Dermiste/Quadricopter/Cartes/InterfacesCapteurs/gyro/LPR430.png

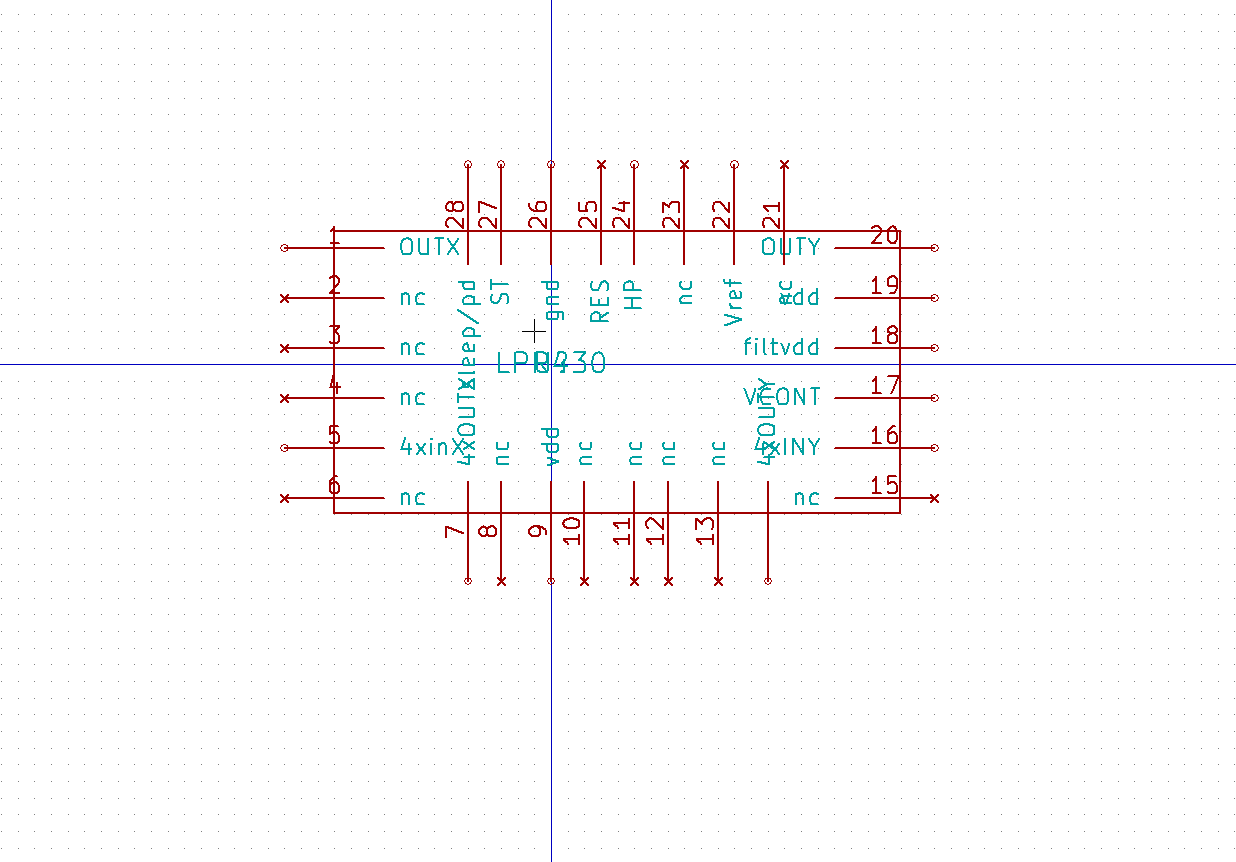
Cartes/InterfacesCapteurs/gyro/LPR430.png
