Dermiste/Quadricopter/ScilabScripts/DataTracer/ScreenShots/noise_2cylinbloc_2normal.png

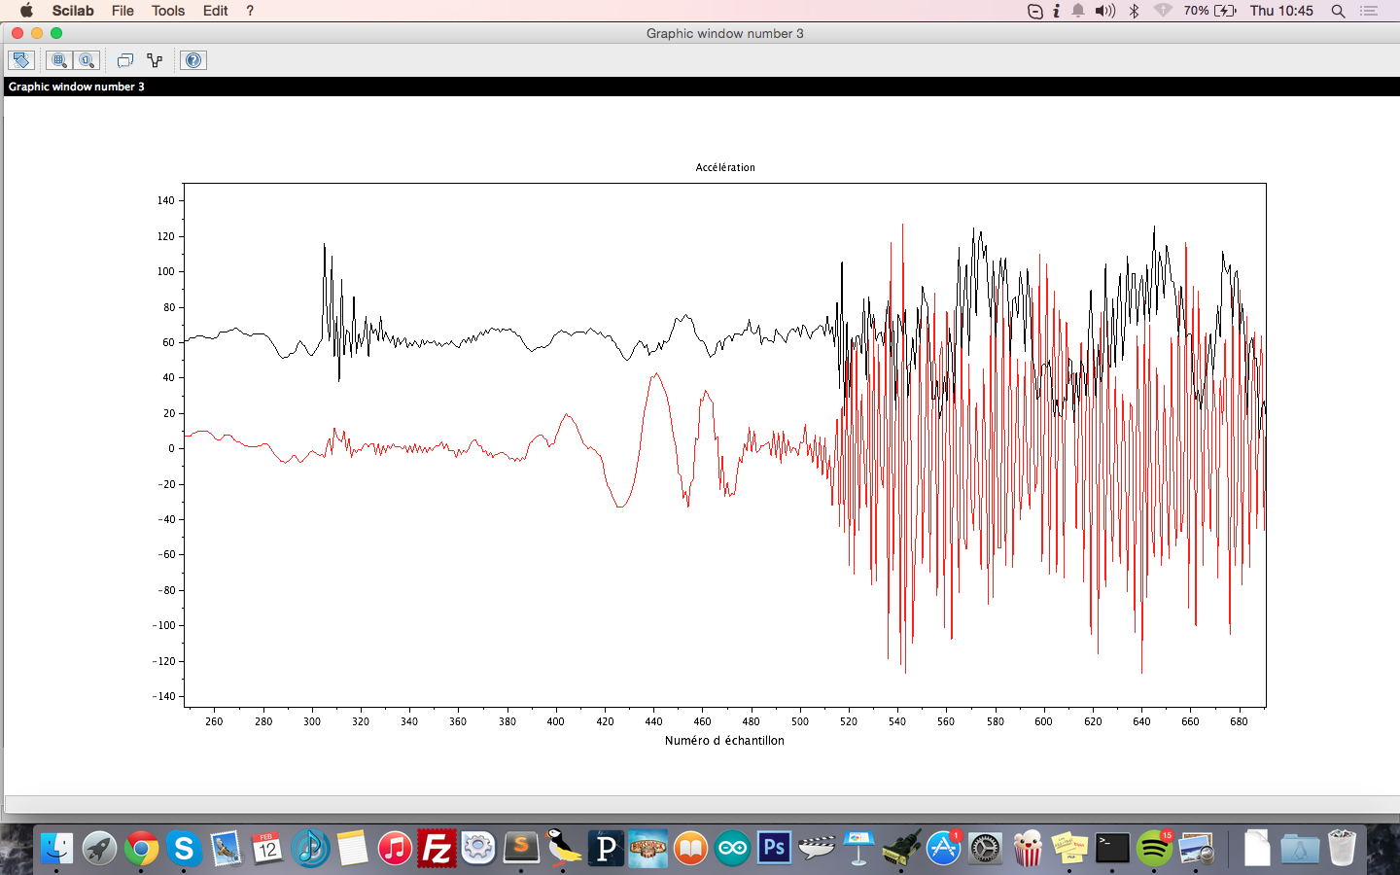
ScilabScripts/DataTracer/ScreenShots/noise_2cylinbloc_2normal.png
