Dermiste/Quadricopter/ScilabScripts/DataTracer/ScreenShots/noise_cylinbloc_axis.png

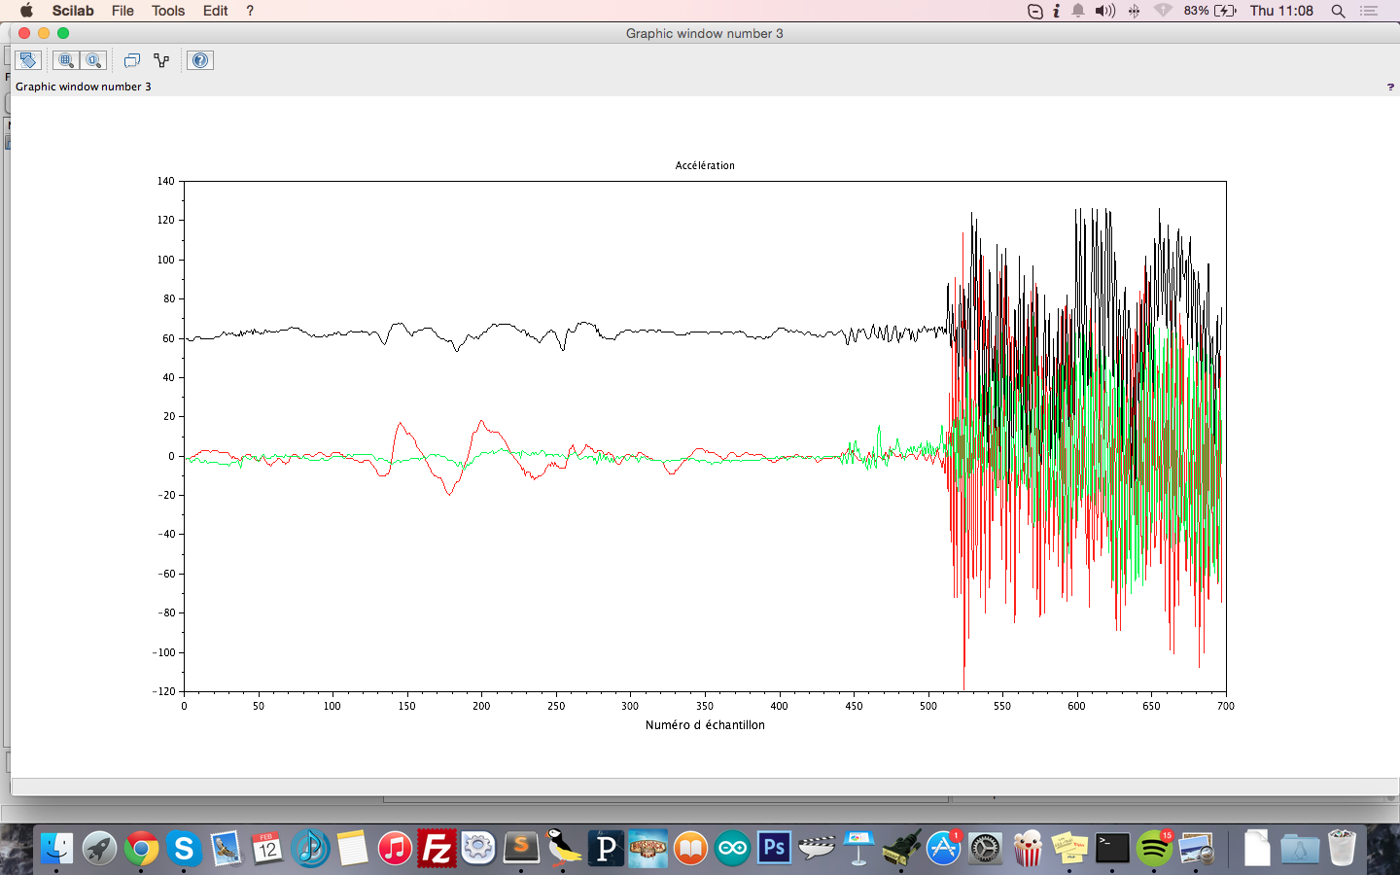
ScilabScripts/DataTracer/ScreenShots/noise_cylinbloc_axis.png
