Dermiste/Quadricopter/ScilabScripts/DataTracer/ScreenShots/noise_each_motor.png

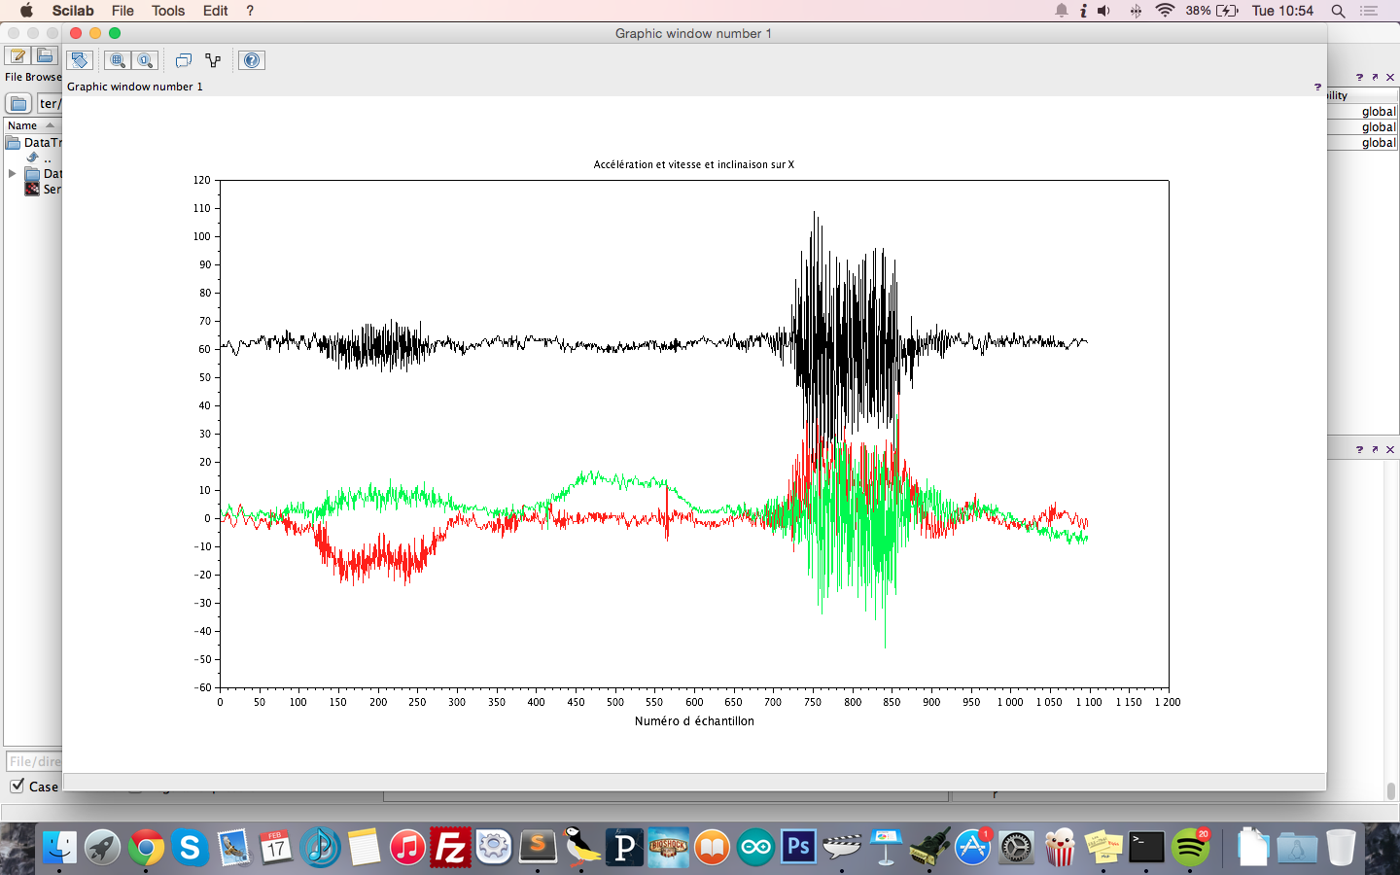
ScilabScripts/DataTracer/ScreenShots/noise_each_motor.png
