Dermiste/Quadricopter/ScilabScripts/DataTracer/ScreenShots/noise_each_motor_2.png

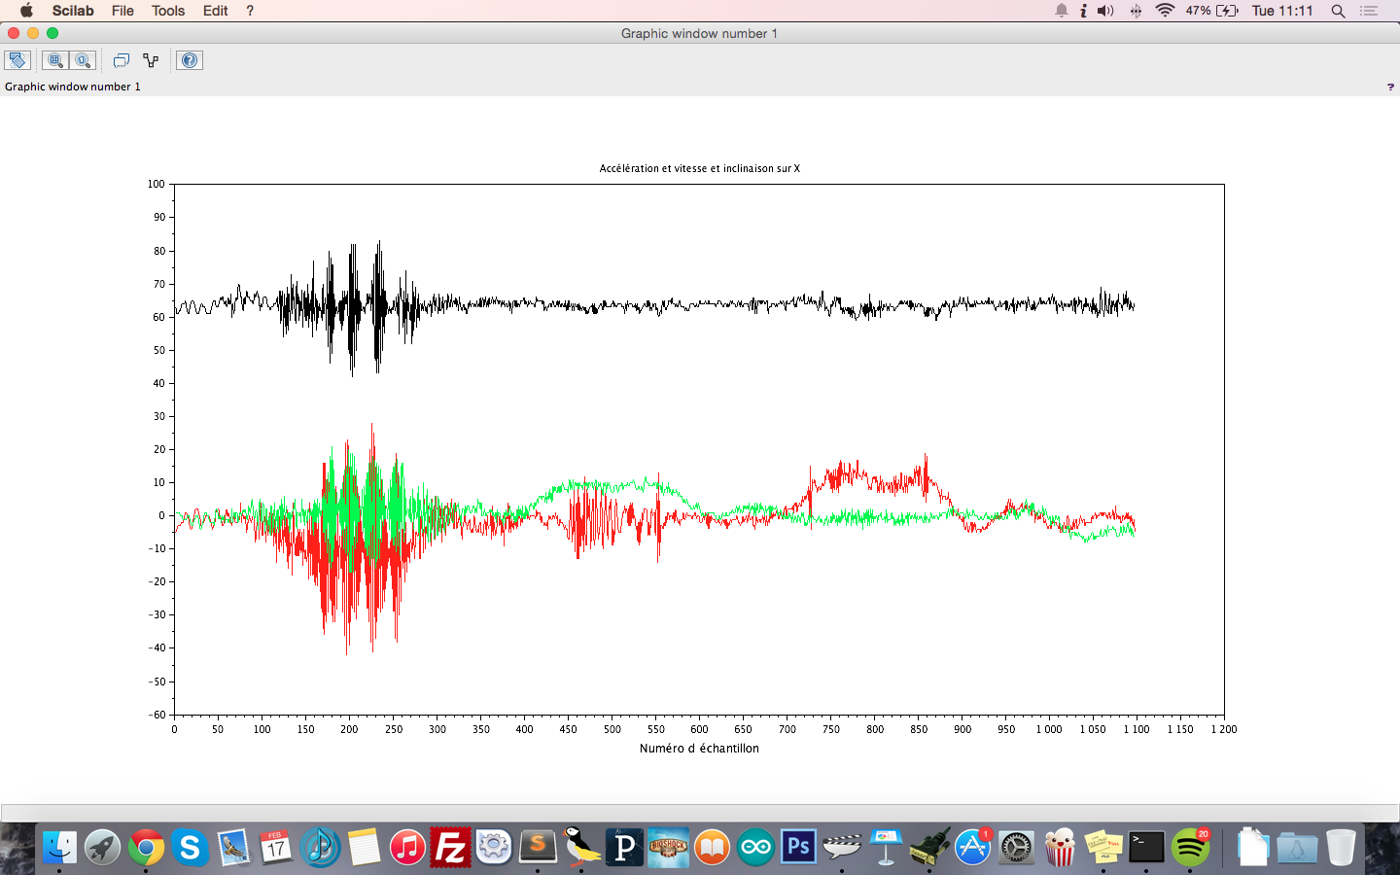
ScilabScripts/DataTracer/ScreenShots/noise_each_motor_2.png
