Dermiste/Quadricopter/ScilabScripts/DataTracer/ScreenShots/noise_normalbloc_axis.png

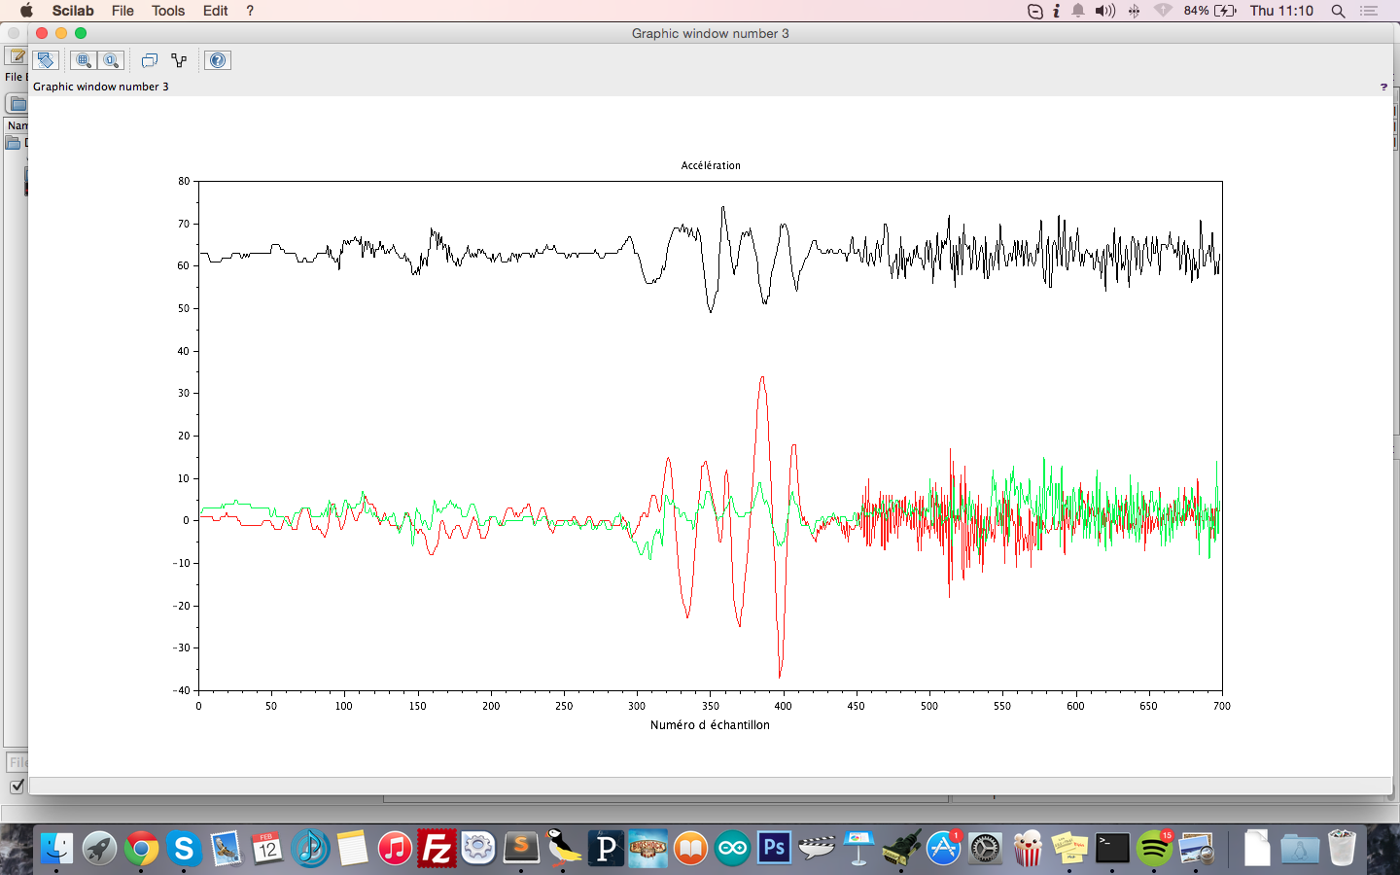
ScilabScripts/DataTracer/ScreenShots/noise_normalbloc_axis.png
