Dermiste/Quadricopter/ScilabScripts/DataTracer/ScreenShots/pitch_complementary.png

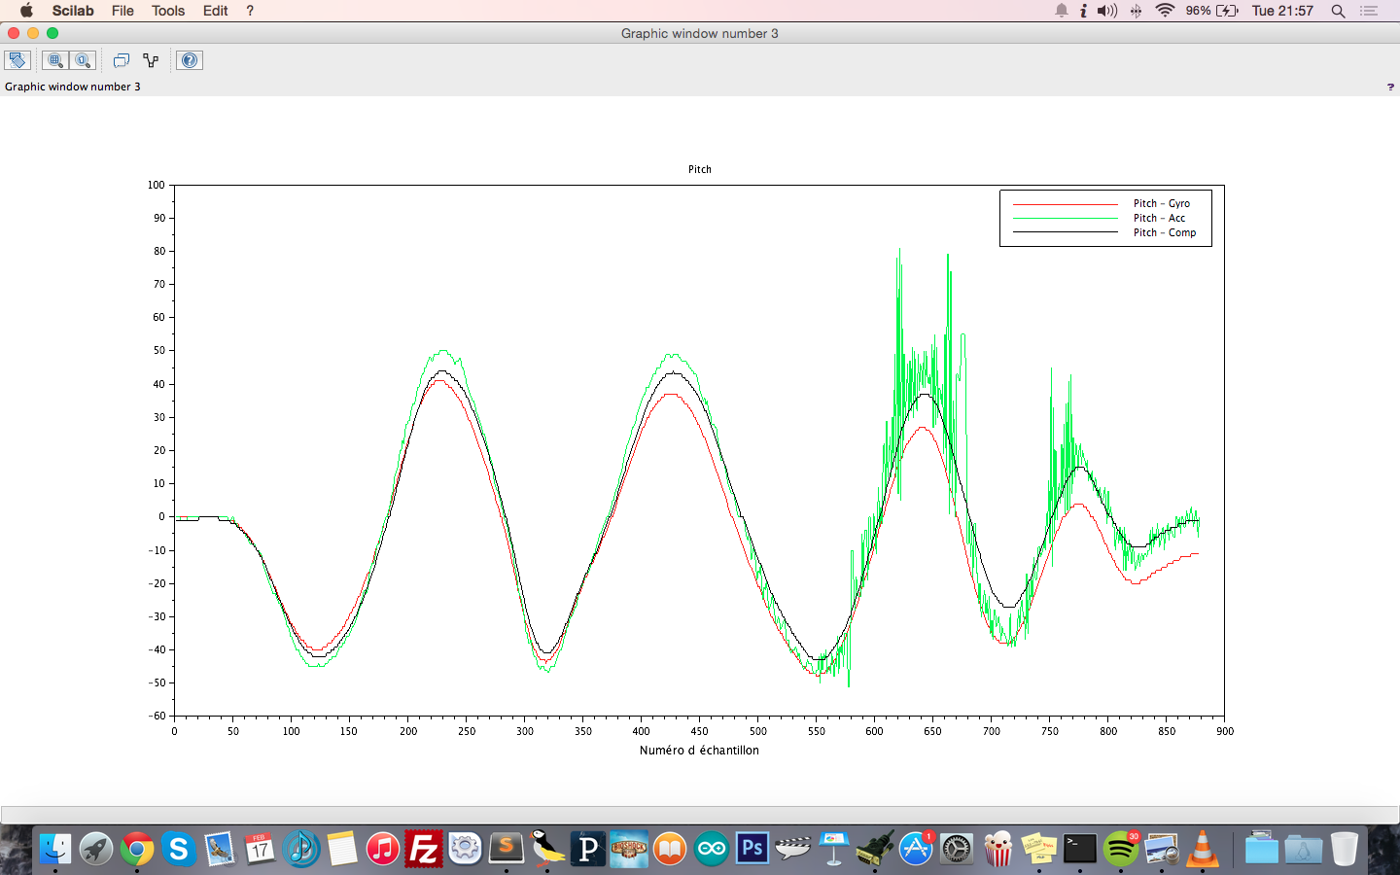
ScilabScripts/DataTracer/ScreenShots/pitch_complementary.png
